Adil-Jussupov/PortableBraille/DataSheets/BrailleLinePic.jpg

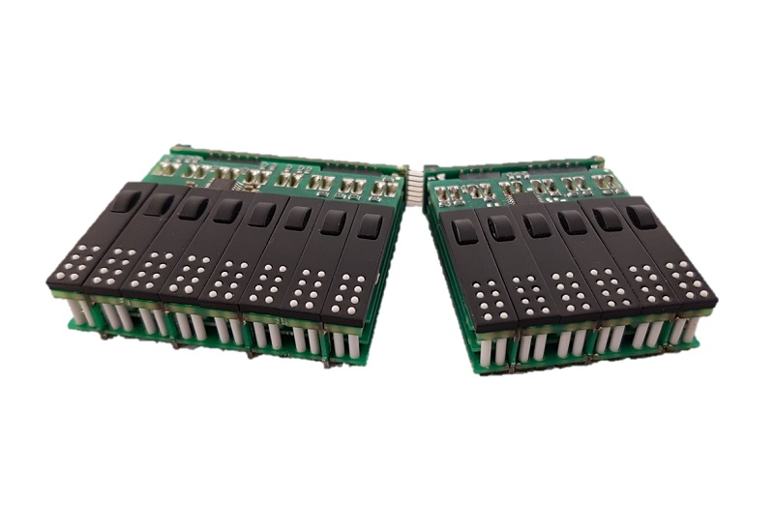
DataSheets/BrailleLinePic.jpg
