Adil-Jussupov/PortableBraille/DataSheets/DC-DC_converter.jpg

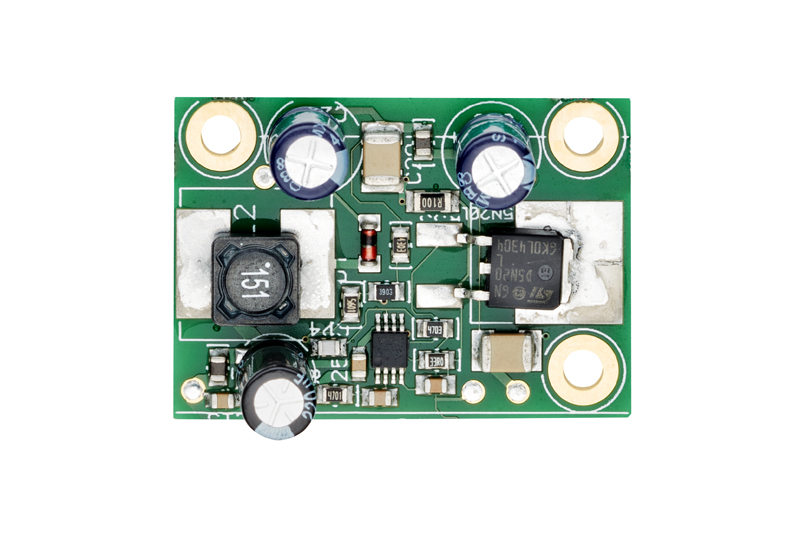
DataSheets/DC-DC_converter.jpg
