Adil-Jussupov/PortableBraille/DataSheets/ESP32_Wroom_dimensions.jpg

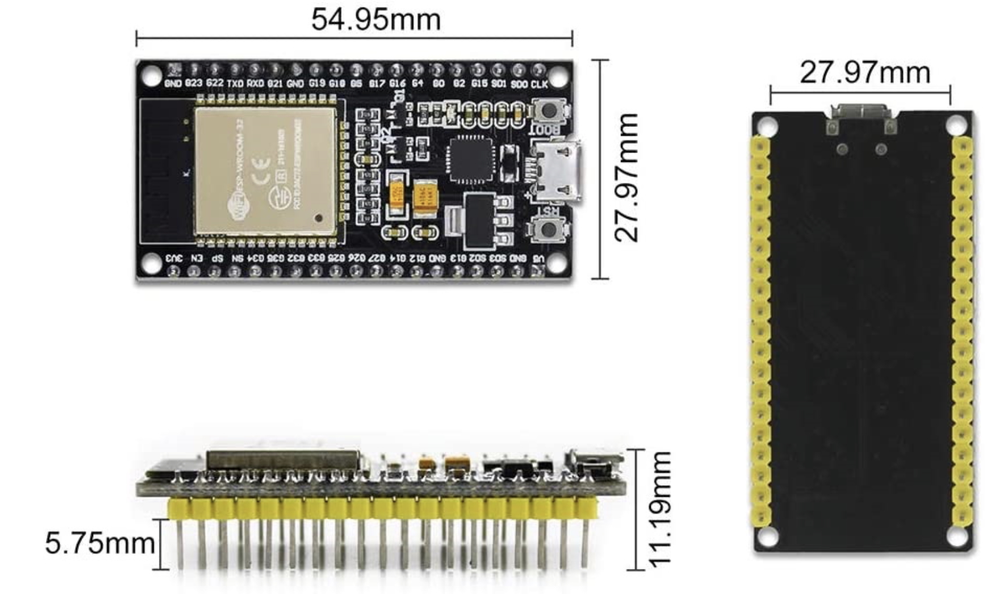
DataSheets/ESP32_Wroom_dimensions.jpg
