Adil-Jussupov/PortableBraille/DataSheets/HiLetgo_Mini_ESP-32_dimensions.jpg

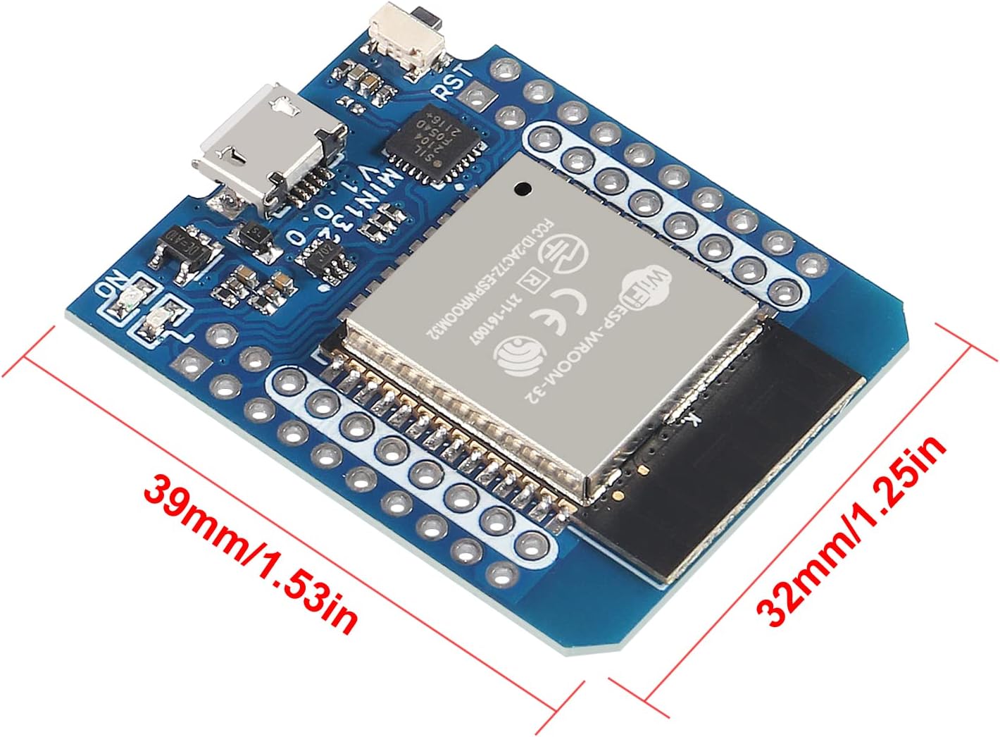
DataSheets/HiLetgo_Mini_ESP-32_dimensions.jpg
