Adil-Jussupov/PortableBraille/DataSheets/iPhone15pro_dimensions.png

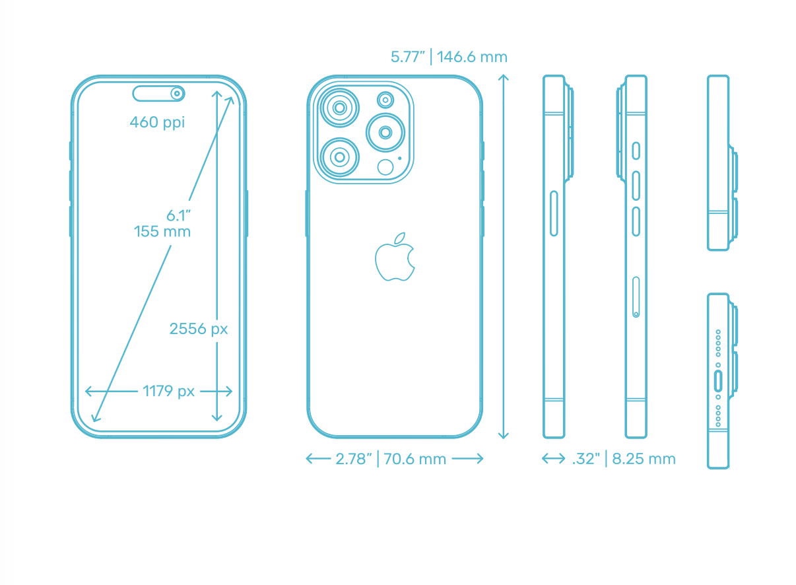
DataSheets/iPhone15pro_dimensions.png
