Adil-Jussupov/PortableBraille/DataSheets/Keypad_dimensions.jpg

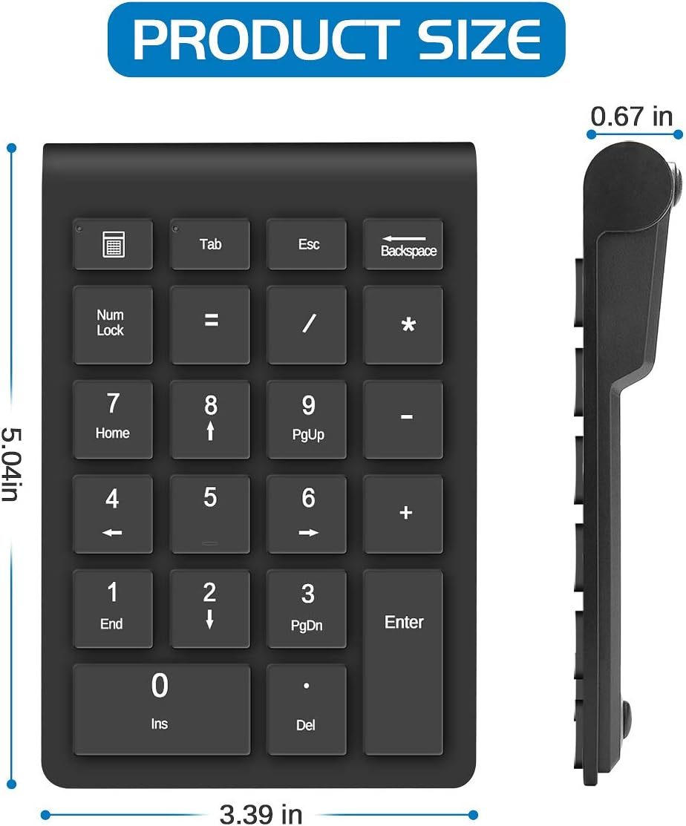
DataSheets/Keypad_dimensions.jpg
