Adil-Jussupov/PortableBraille/DataSheets/Li-Po_battery.jpg

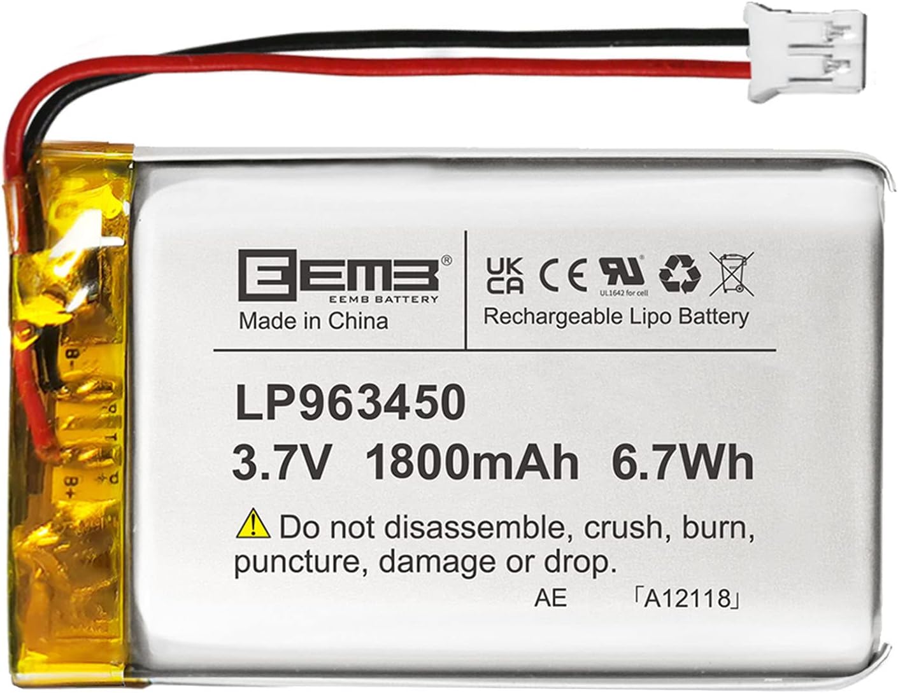
DataSheets/Li-Po_battery.jpg
