Adil-Jussupov/PortableBraille/DataSheets/MagSafe_magnet_ring.jpg

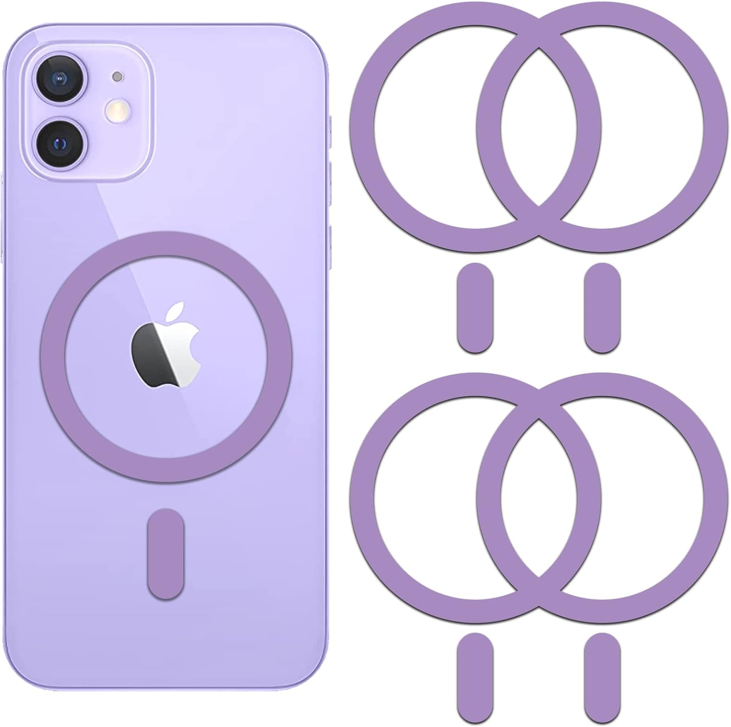
DataSheets/MagSafe_magnet_ring.jpg
