Adil-Jussupov/PortableBraille/DataSheets/NRF52840_dimenstions.png

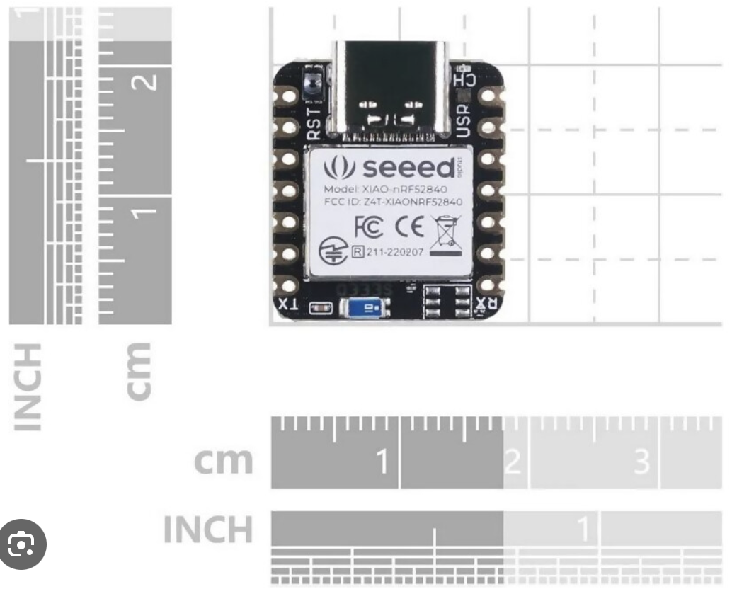
DataSheets/NRF52840_dimenstions.png
