Adil-Jussupov/PortableBraille/DataSheets/TP4056.jpg

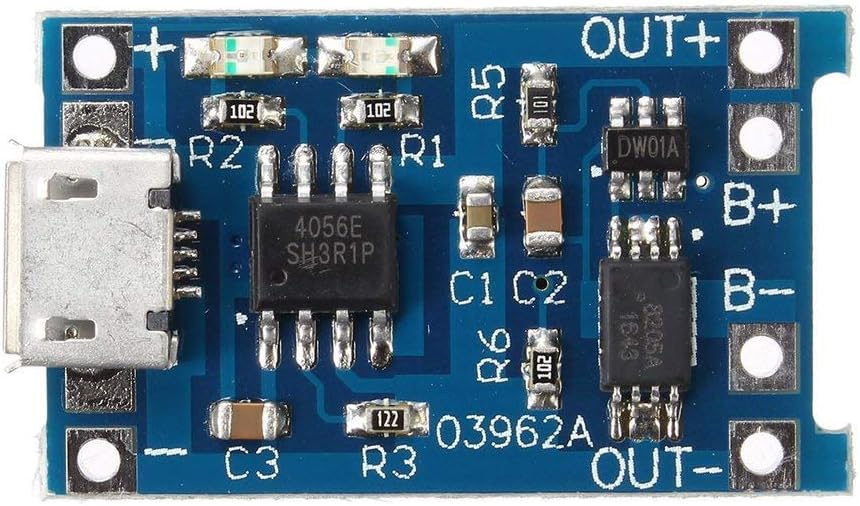
DataSheets/TP4056.jpg
