Adil-Jussupov/PortableBraille/Pitch_Deck/Block_diagram.jpg

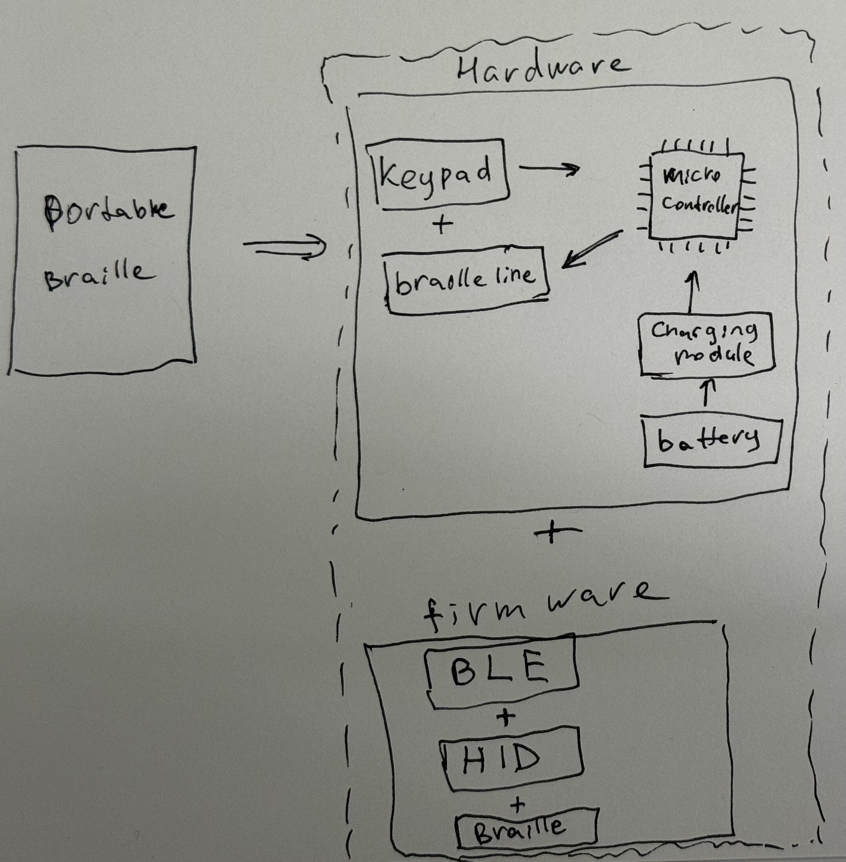
Pitch_Deck/Block_diagram.jpg
