Adil-Jussupov/PortableBraille/Enclosure/Standard_Parts/ESP32-WROOM.SLDPRT

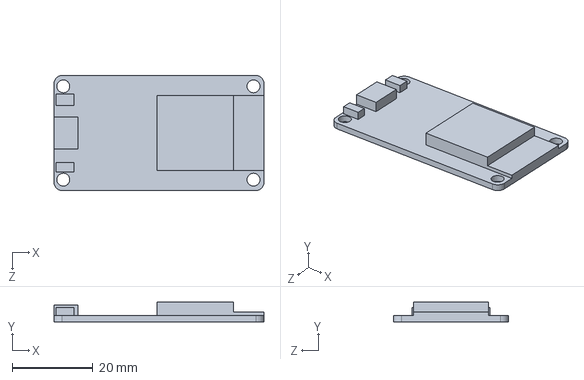
[picture p31: CAD file, 2025-02-15]
Enclosure/Standard_Parts/ESP32-WROOM.SLDPRT
52.0 x 4.90 x 28.5 mm
