Adil-Jussupov/PortableBraille/Enclosure/Standard_Parts/Mini-ESP32.SLDPRT

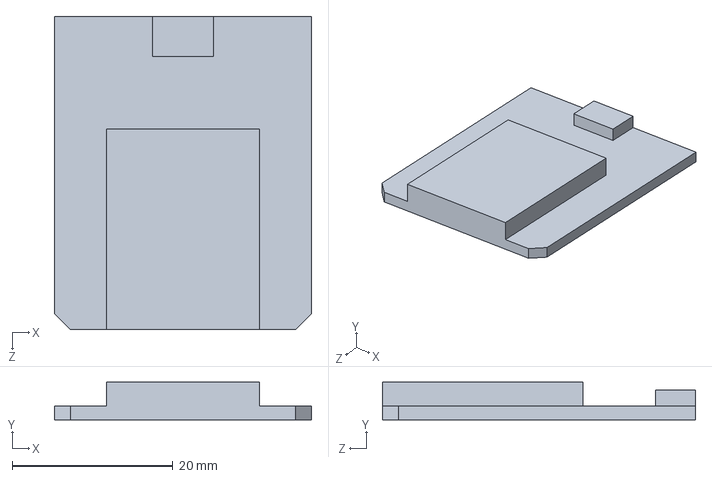
[picture p32: CAD file, 2025-02-15]
Enclosure/Standard_Parts/Mini-ESP32.SLDPRT
32.0 x 4.70 x 39.0 mm
