Adil-Jussupov/PortableBraille/Firmware/FirmwarePortableBraille/brailleconst.cpp

// brailleConst.cpp

#include "brailleconst.h"

const int asciiCodes[] = {
  32,
  32,
  32,
  32,
  15,
  46,
  32,
  32,
  39,
  45,
  42,
  32,
  47,
  32,
  124,
  35,
  44,
  32,
  58,
  46,
  105,
  32,
  106,
  119,
  59,
  63,
  33,
  32,
  115,
  32,
  116,
  41,
  97,
  32,
  101,
  32,
  99,
  32,
  100,
  32,
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
};

const char toText[] = {
  '0',
  '0',
  '0',
  '0',
  '0',
  '0',
  '$',
  '0',
  '0',
  '0',
  '0',
  '0',
  '0',
  '0',
  '0',
  '0',
  '0',
  '0',
  '0',
  'i',
  '*',
  'j',
  '0',
  '0',
  '0',
  '0',
  '0',
  's',
  '0',
  't',
  '0',
  'a',
  '0',
  'e',
  '0',
  'c',
  '0',
  'd',
  '0',
  'k',
  'u',
  'o',
  'y',
  'm',
  'w',
  'n',
  'x',
  'b',
  '0',
  'h',
  '0',
  'f',
  '0',
  'g',
  '0',
  'l',
  'v',
  'r',
  '0',
  'p',
  'z',
  'q',
  '@',
};
